OLIMEX/RT1010Py/DOCUMENTS/RT1010-py-board.png

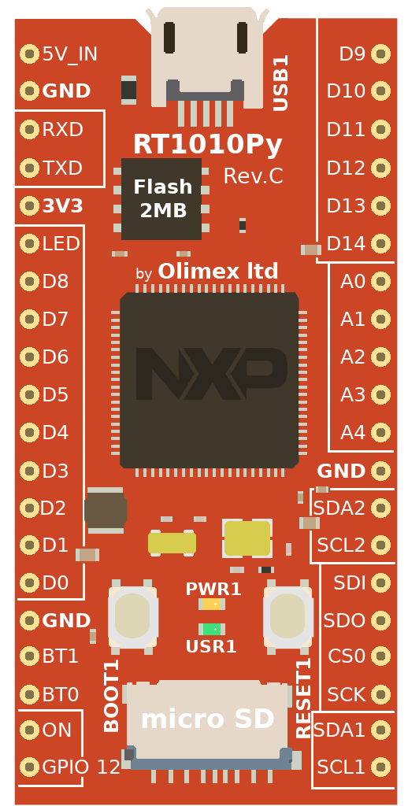
DOCUMENTS/RT1010-py-board.png
