OLIMEX/RT1010Py/SOFTWARE/I2S-RT1010py-to-MAX98357A.jpg

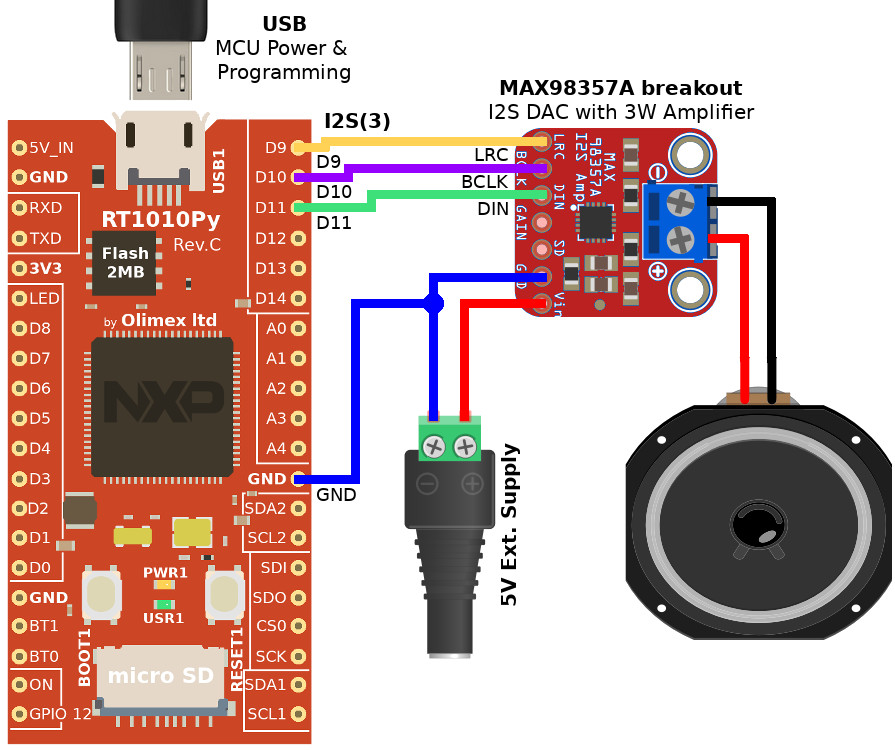
SOFTWARE/I2S-RT1010py-to-MAX98357A.jpg
