OLIMEX/RT1010Py/SOFTWARE/onewire-RT1010py-to-ds18b20.jpg

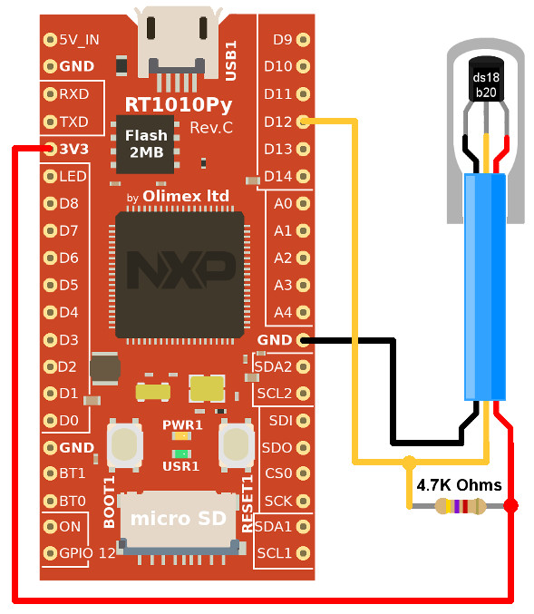
SOFTWARE/onewire-RT1010py-to-ds18b20.jpg
